jonbuford/atomo-all-boards/CM_M2K22_A/prod/CM_M2K22_A-F.Mask.pdf

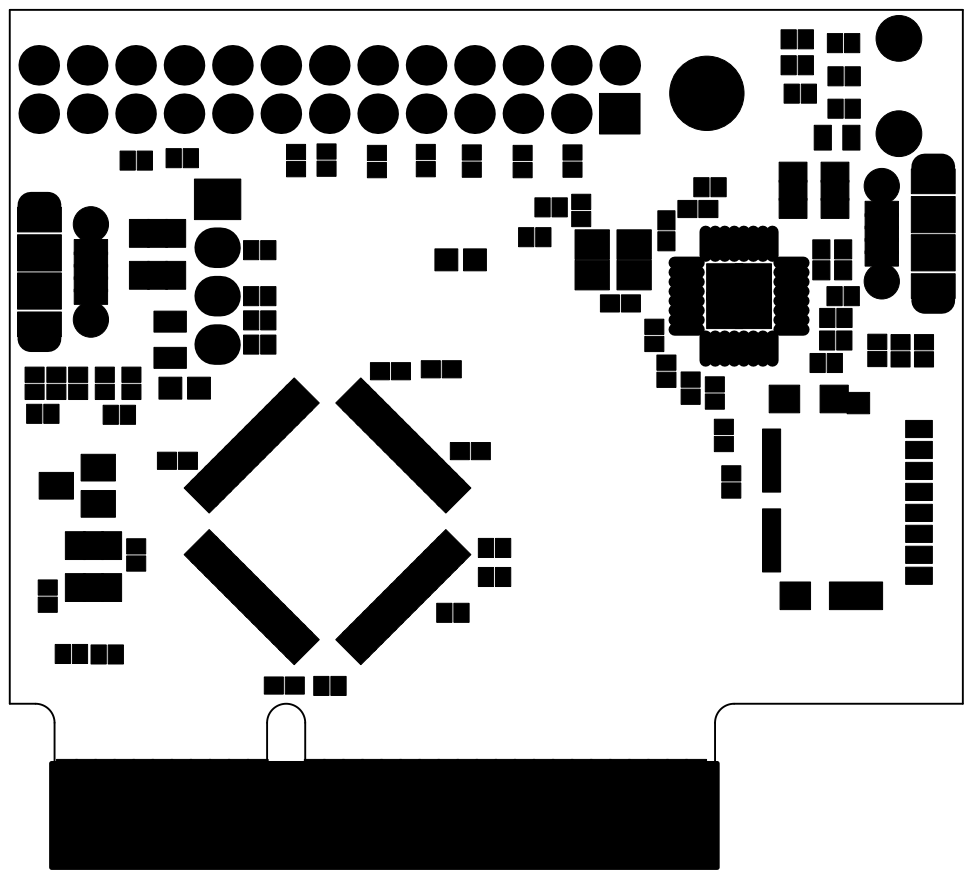
[picture p11: page 1]
