jonbuford/atomo-all-boards/CM_M2K22_A/prod/CM_M2K22_A-F.Paste.pdf

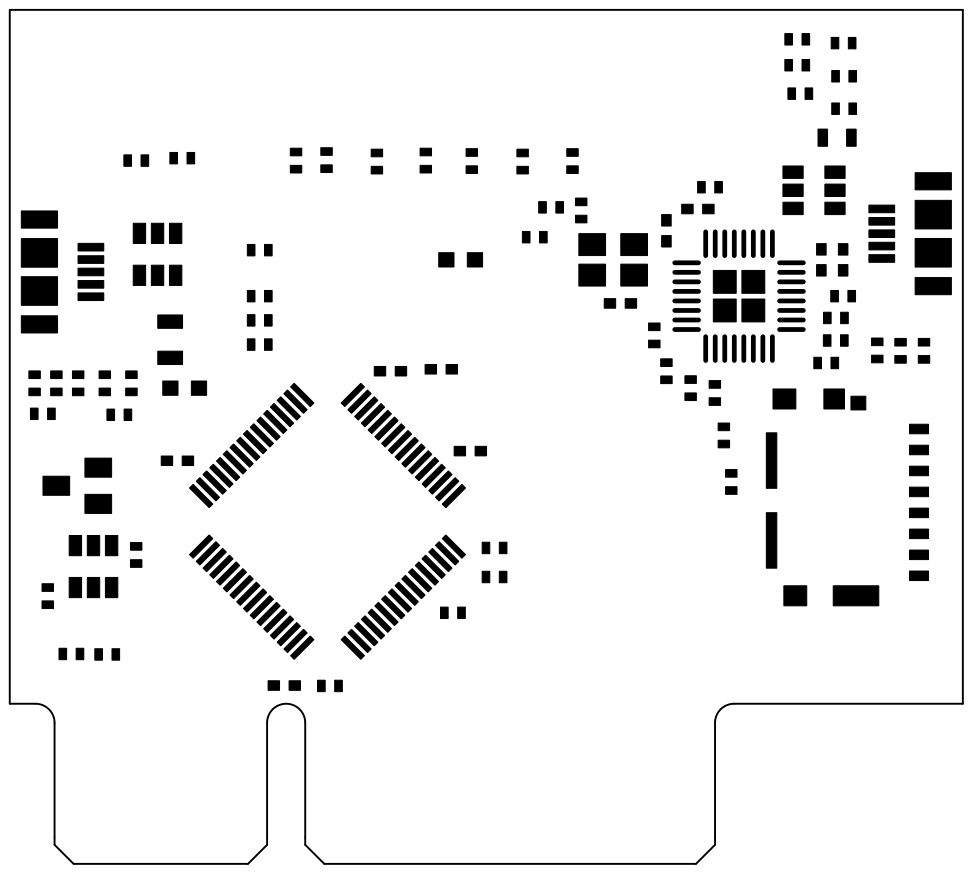
[picture p12: page 1]
