jonbuford/atomo-all-boards/CM_M2K22_A/prod/CM_M2K22_A-F.SilkS.pdf

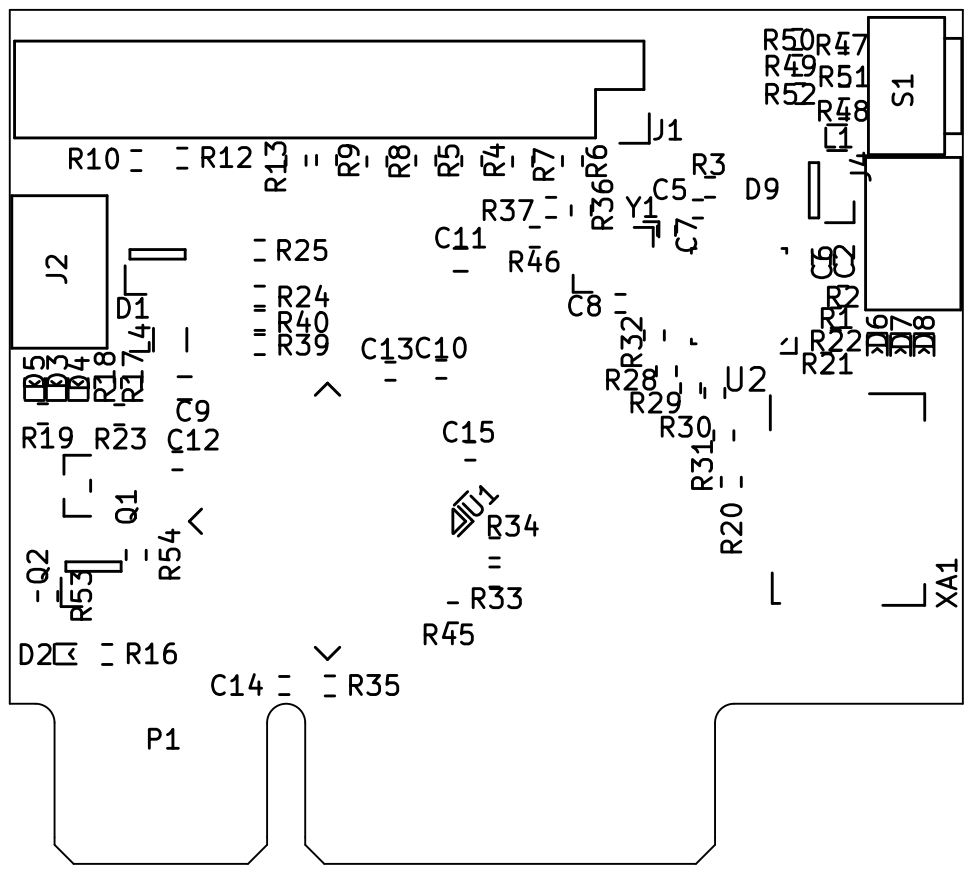
[picture p13: page 1]
