jonbuford/atomo-all-boards/CM_M2K22_A/prod/CM_M2K22_A-In1.Cu.pdf

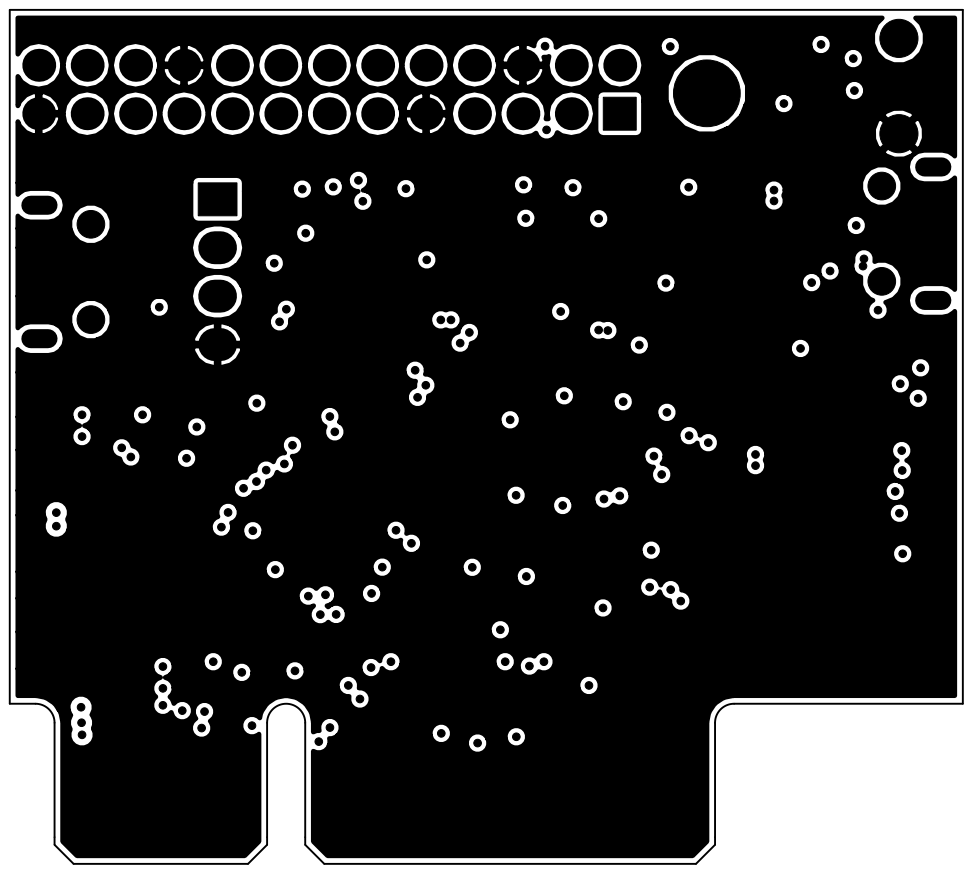
[picture p14: page 1]
