jonbuford/atomo-all-boards/CM_M2K22_A/prod/CM_M2K22_A-In2.Cu.pdf

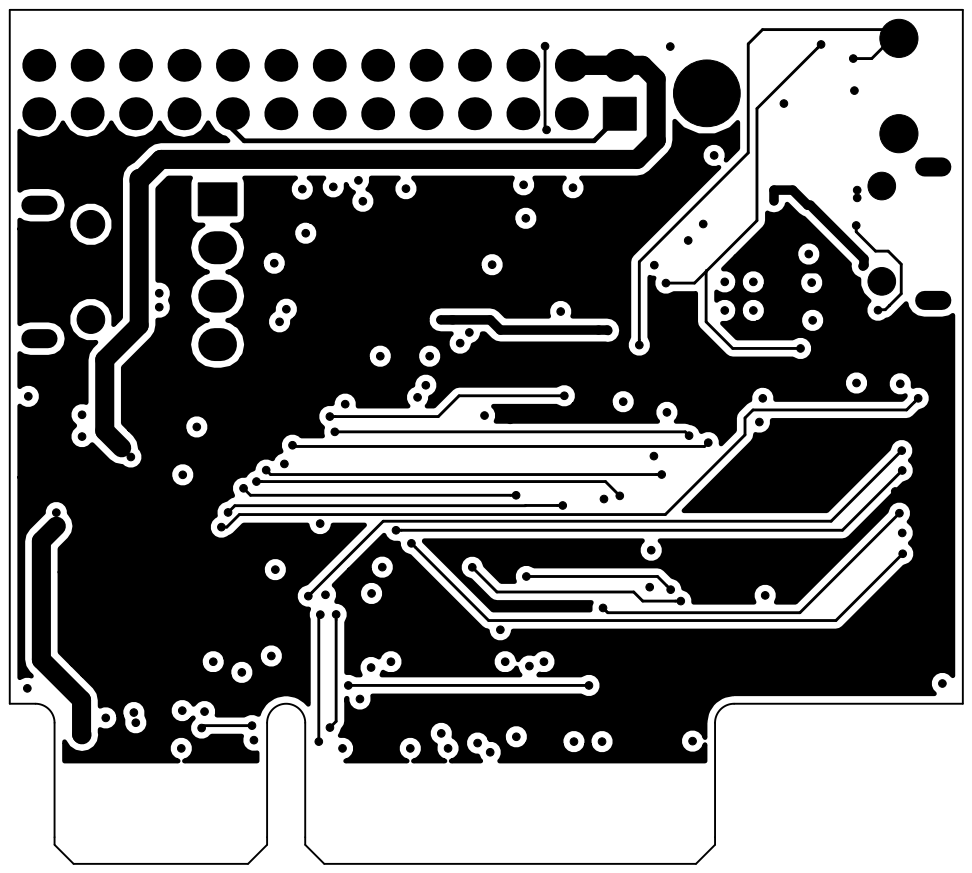
[picture p15: page 1]
