jonbuford/atomo-all-boards/CM_M4K64_A/prod/CM_M4K64_A-B.Adhes.pdf

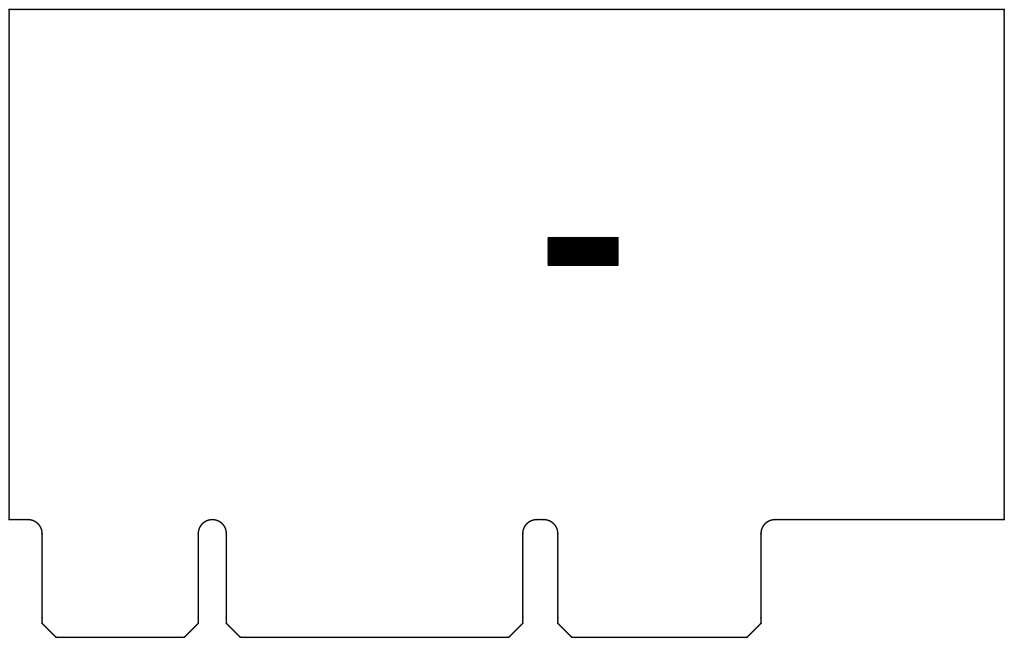
[picture p16: page 1]
