jonbuford/atomo-all-boards/CM_M4K64_A/prod/CM_M4K64_A-B.Cu.pdf

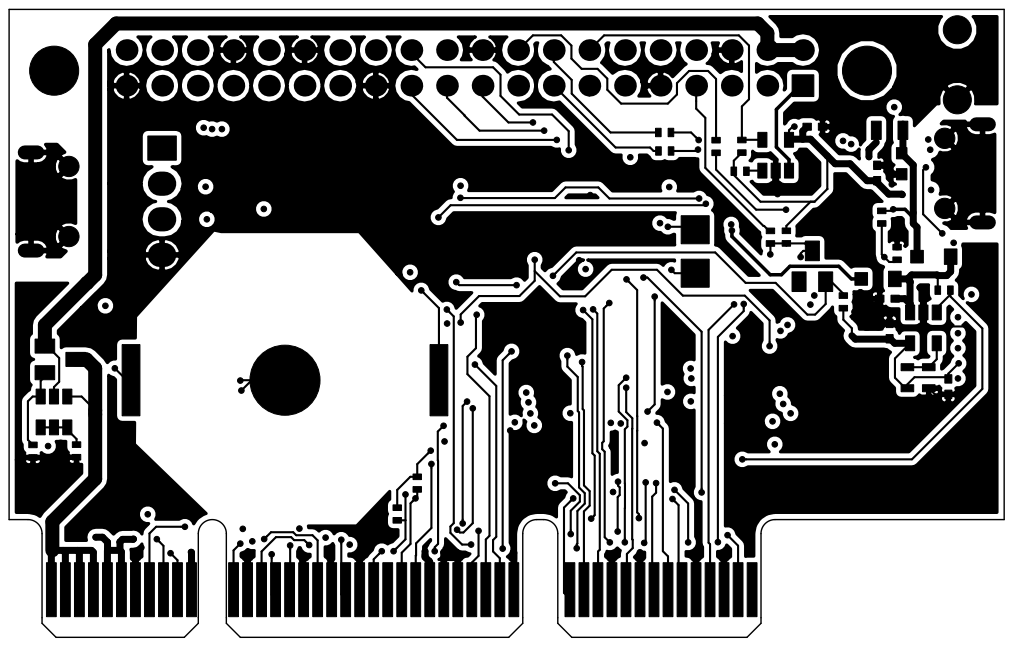
[picture p17: page 1]
