jonbuford/atomo-all-boards/CM_M4K64_A/prod/CM_M4K64_A-B.Mask.pdf

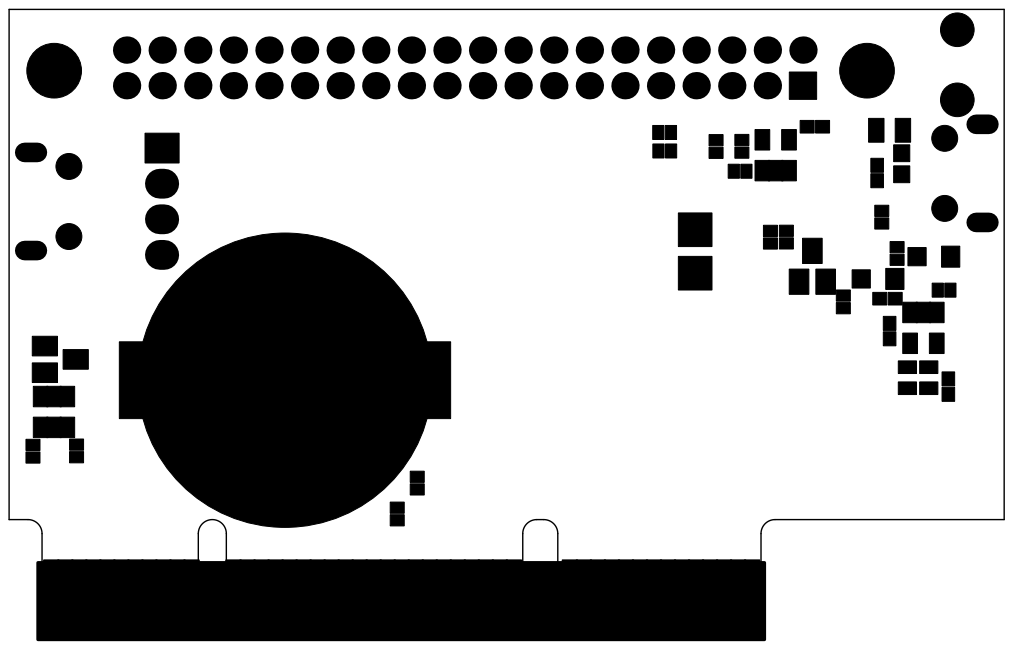
[picture p18: page 1]
