jonbuford/atomo-all-boards/CM_M4K64_A/prod/CM_M4K64_A-B.Paste.pdf

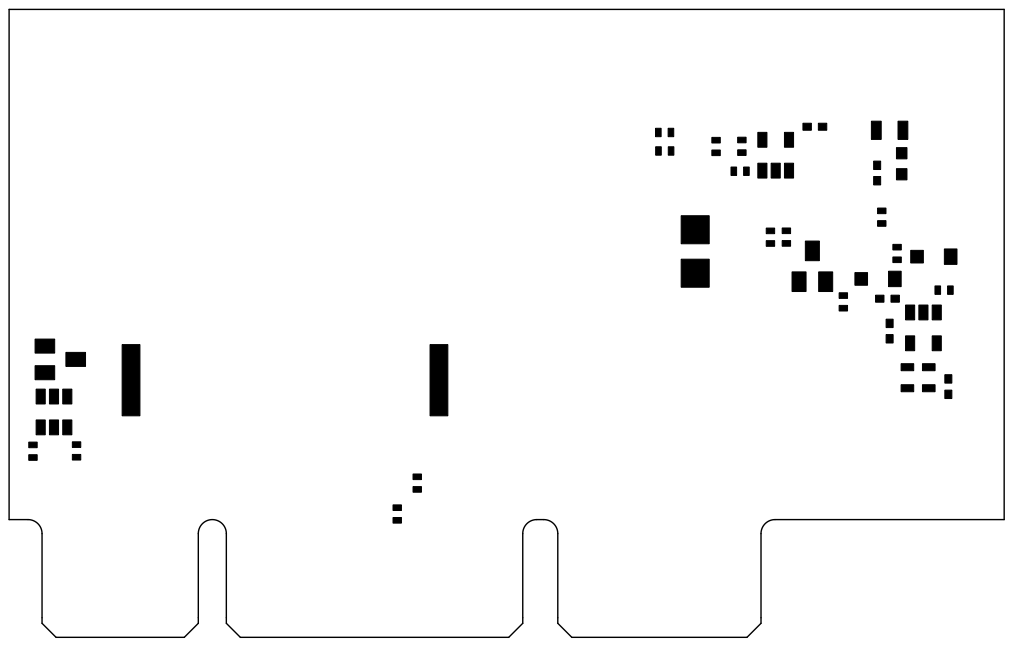
[picture p19: page 1]
