jonbuford/atomo-all-boards/CM_M4K64_A/prod/CM_M4K64_A-B.SilkS.pdf

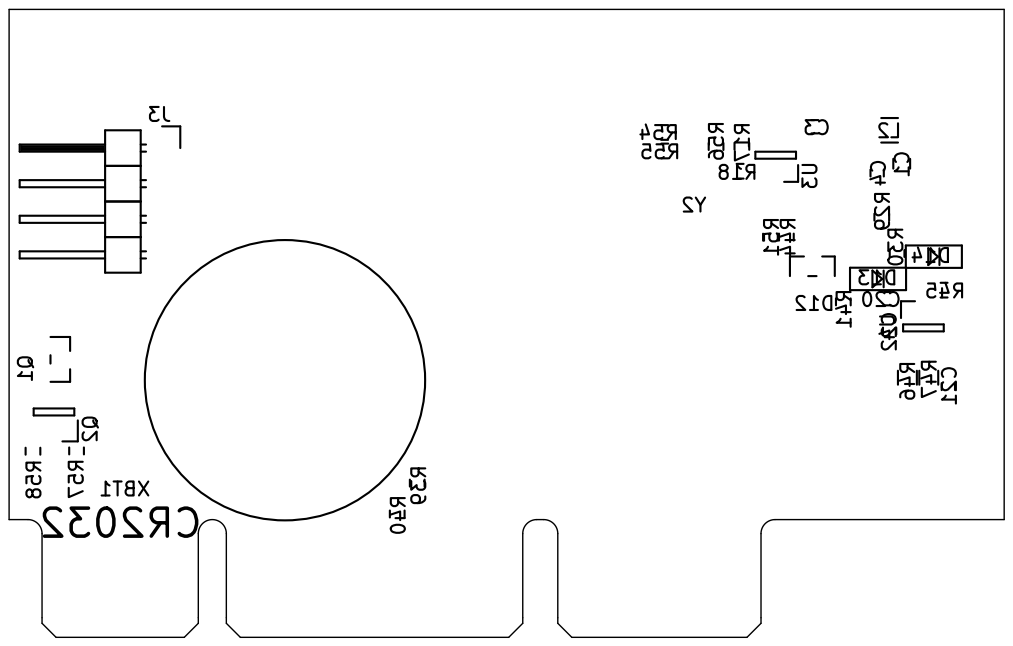
[picture p20: page 1]
