jonbuford/atomo-all-boards/CM_M4K64_A/prod/CM_M4K64_A-Edge.Cuts.pdf

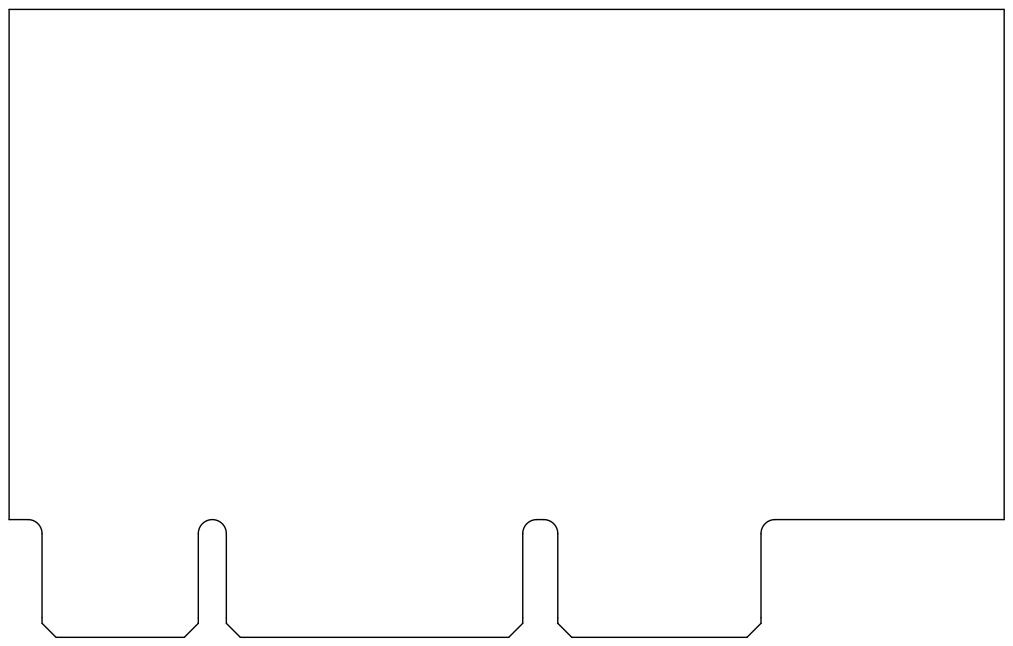
[picture p21: page 1]
