jonbuford/atomo-all-boards/CM_M4K64_A/prod/CM_M4K64_A-F.Cu.pdf

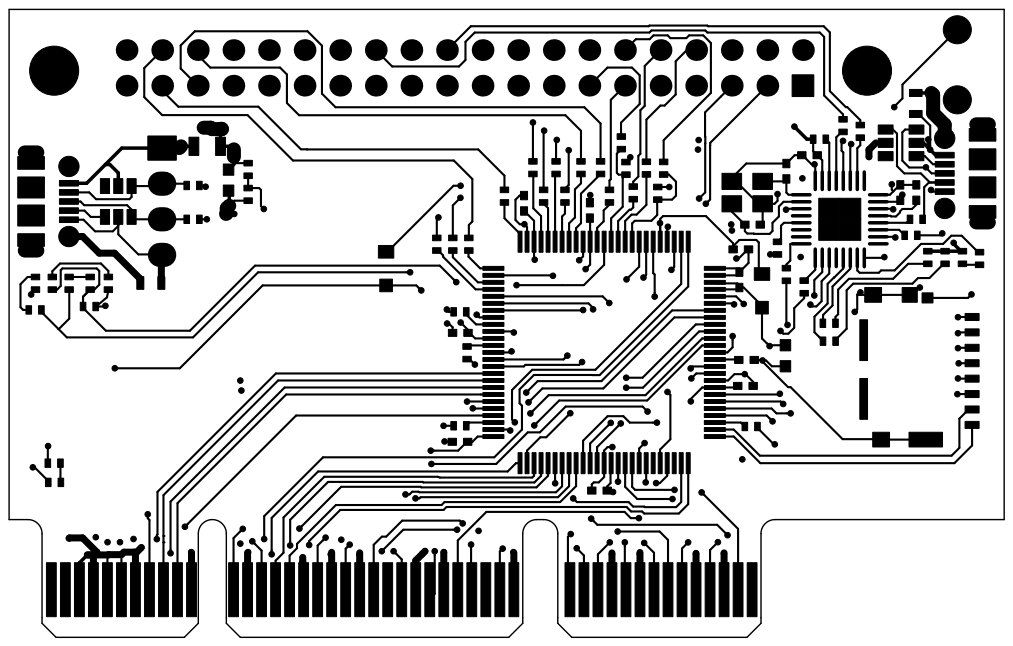
[picture p22: page 1]
