jonbuford/atomo-all-boards/CM_M4K64_A/prod/CM_M4K64_A-F.Mask.pdf

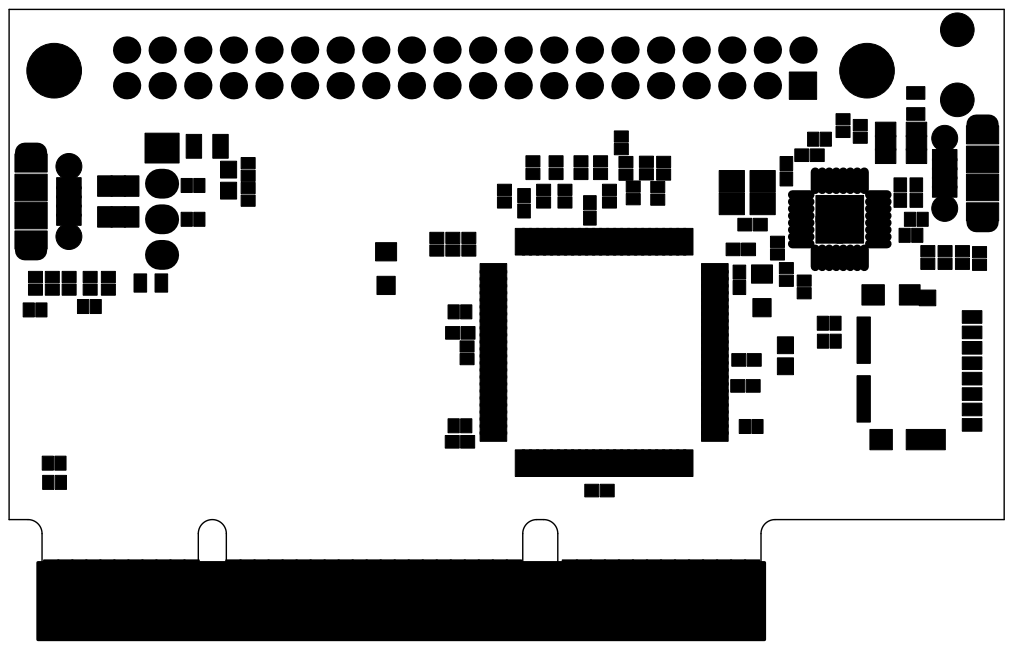
[picture p23: page 1]
