jonbuford/atomo-all-boards/CM_M4K64_A/prod/CM_M4K64_A-F.Paste.pdf

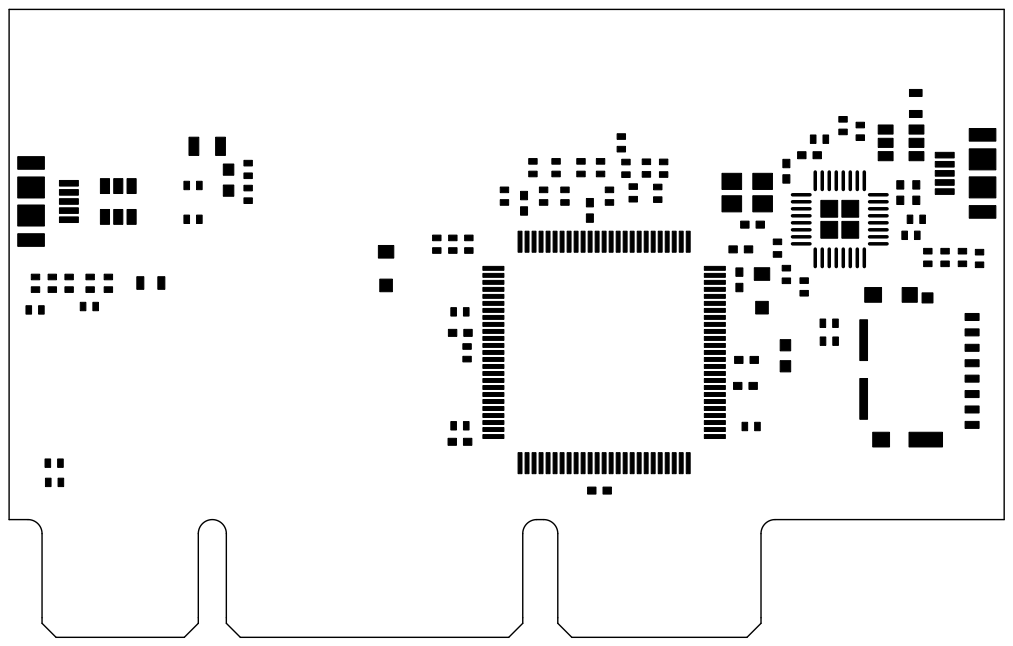
[picture p24: page 1]
