jonbuford/atomo-all-boards/CM_M4K64_A/prod/CM_M4K64_A-F.SilkS.pdf

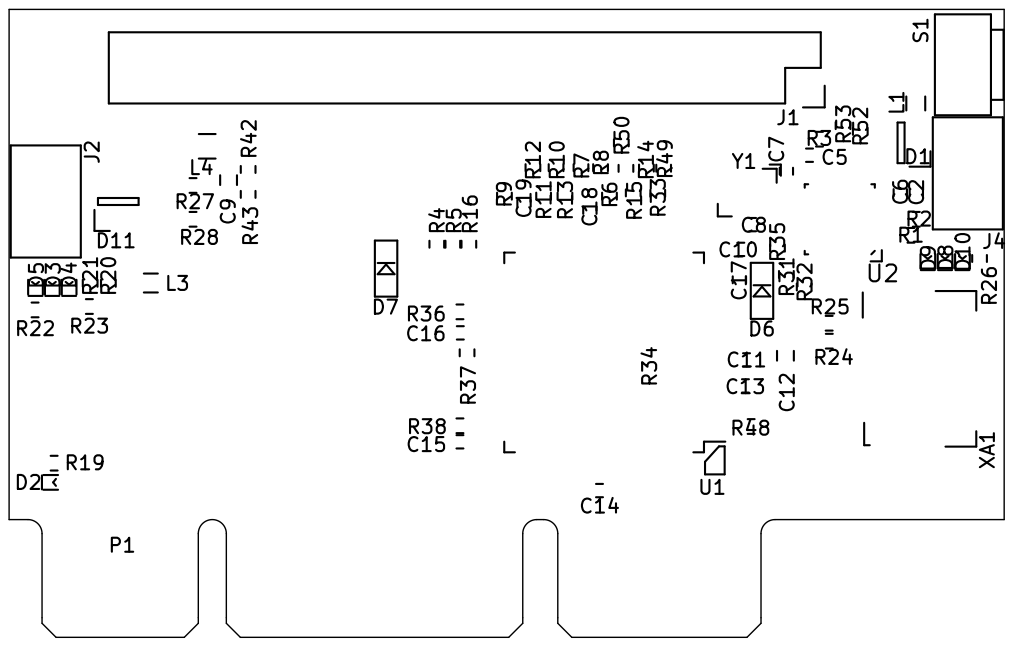
[picture p25: page 1]
