jonbuford/atomo-all-boards/CM_M4K64_A/prod/CM_M4K64_A-In1.Cu.pdf

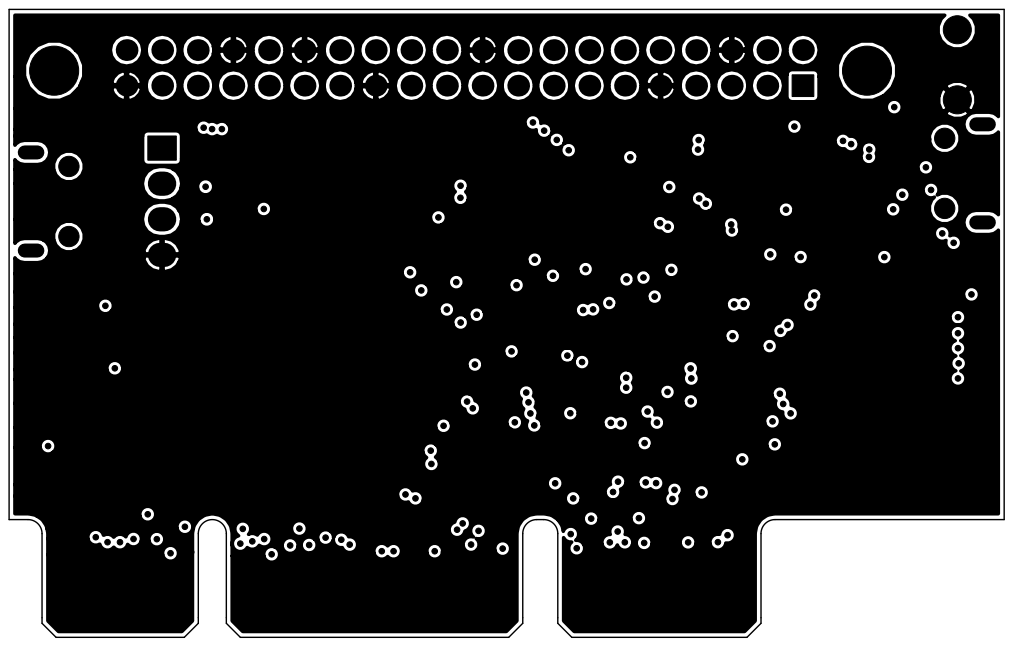
[picture p26: page 1]
