jonbuford/atomo-all-boards/CM_M4K64_A/prod/CM_M4K64_A-In2.Cu.pdf

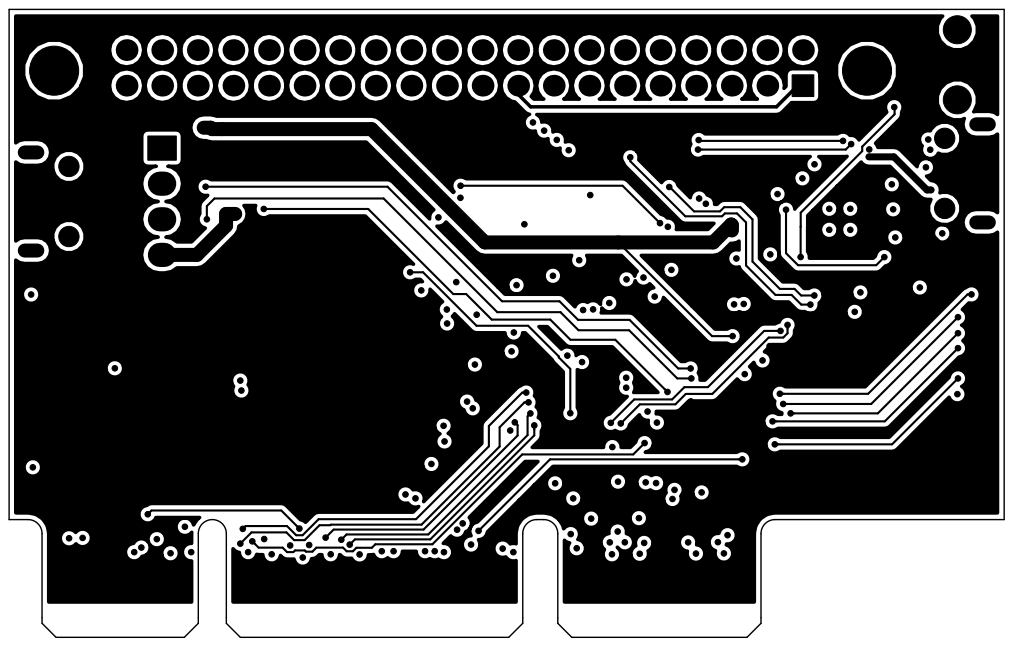
[picture p27: page 1]
