jonbuford/atomo-all-boards/CM_M8K64_A/prod/CM_M8K64_A-B.Adhes.pdf

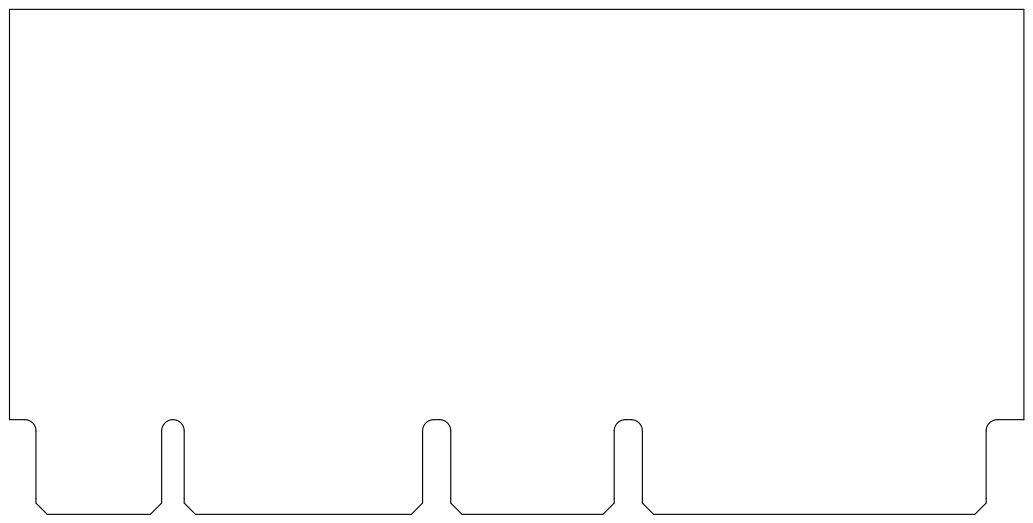
[picture p28: page 1]
