jonbuford/atomo-all-boards/CM_M8K64_A/prod/CM_M8K64_A-B.Cu.pdf

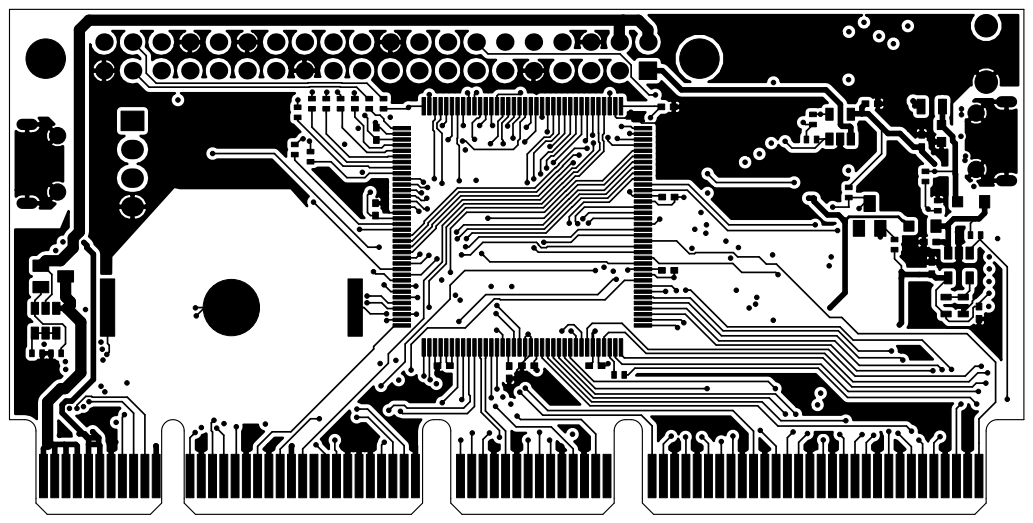
[picture p29: page 1]
