jonbuford/atomo-all-boards/CM_M8K64_A/prod/CM_M8K64_A-B.Mask.pdf

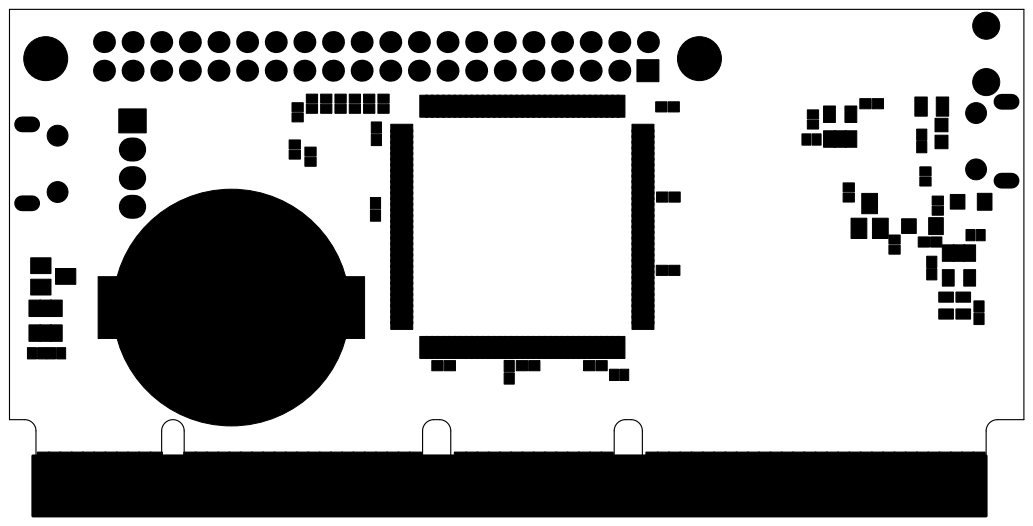
[picture p30: page 1]
