jonbuford/atomo-all-boards/CM_M8K64_A/prod/CM_M8K64_A-B.Paste.pdf

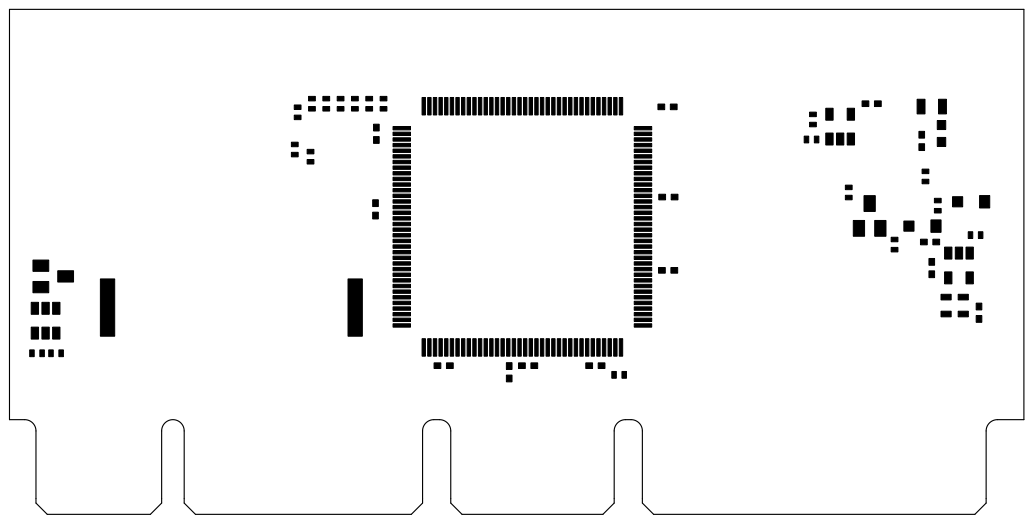
[picture p31: page 1]
