jonbuford/atomo-all-boards/CM_M8K64_A/prod/CM_M8K64_A-B.SilkS.pdf

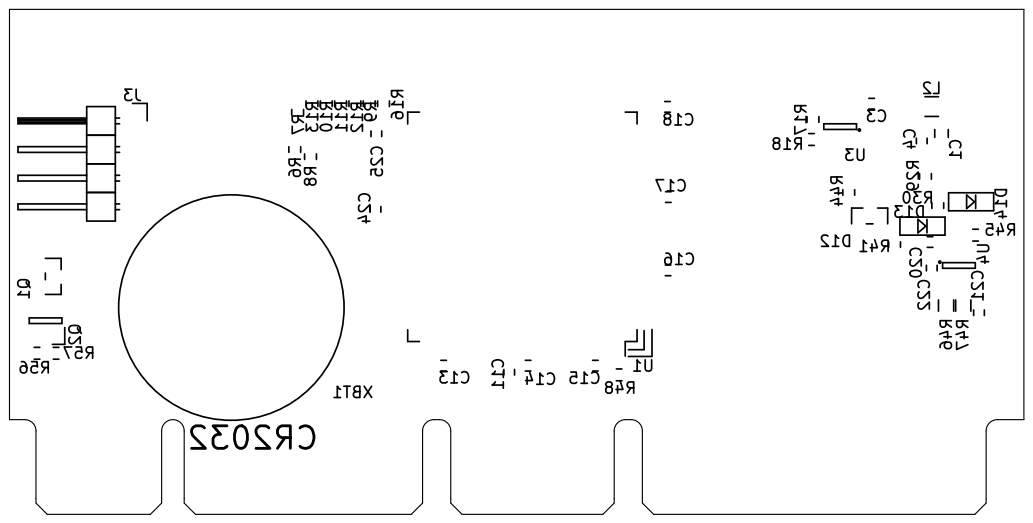
[picture p32: page 1]
