jonbuford/atomo-all-boards/CM_M8K64_A/prod/CM_M8K64_A-F.Adhes.pdf

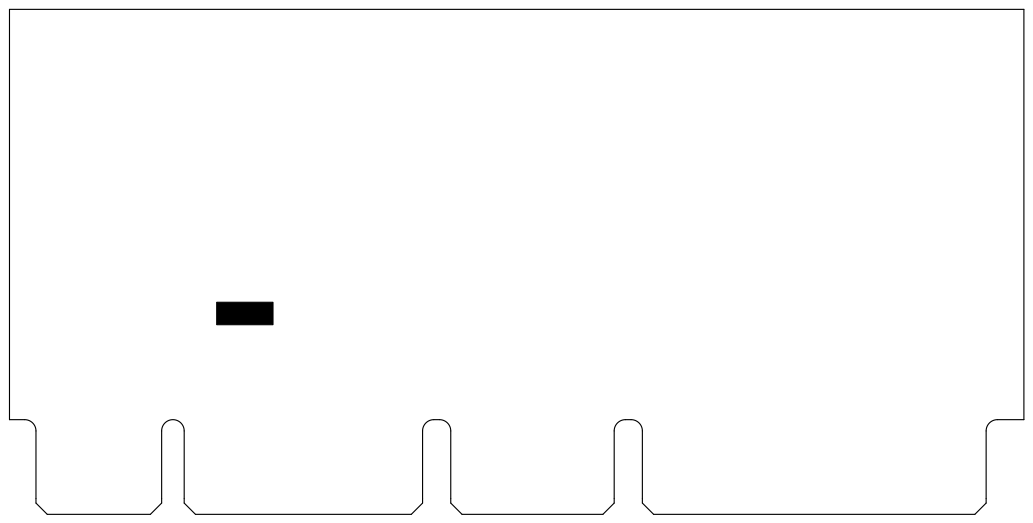
[picture p33: page 1]
