jonbuford/atomo-all-boards/CM_M8K64_A/prod/CM_M8K64_A-F.Cu.pdf

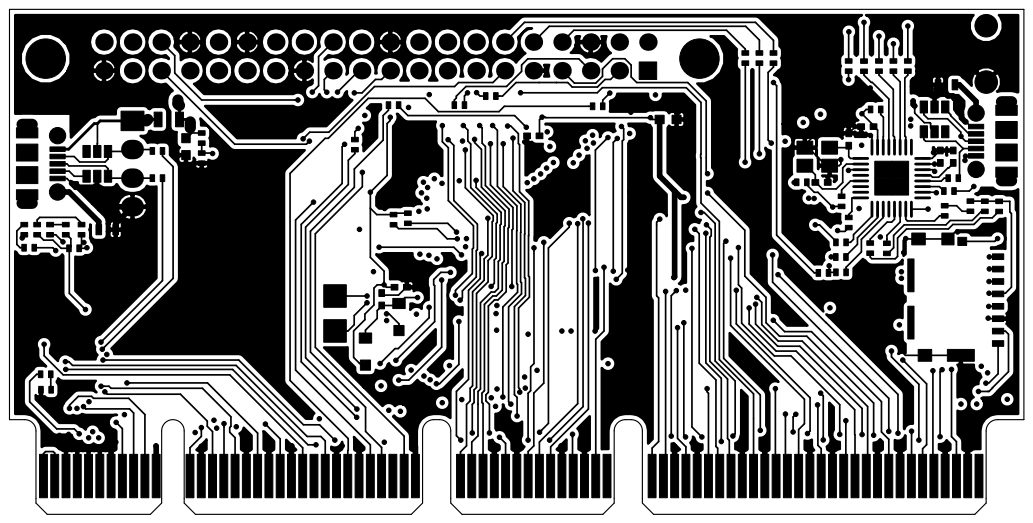
[picture p34: page 1]
