jonbuford/atomo-all-boards/CM_M8K64_A/prod/CM_M8K64_A-F.Mask.pdf

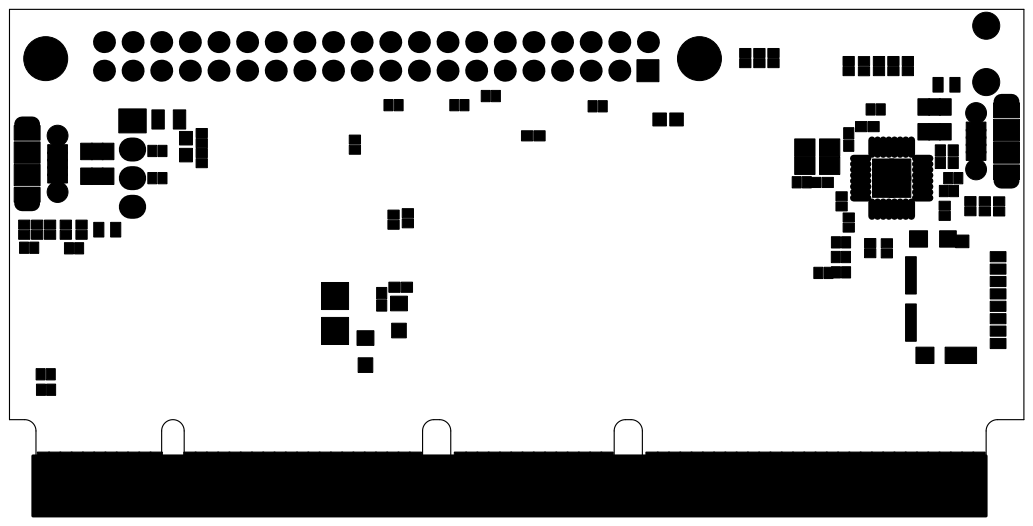
[picture p35: page 1]
