jonbuford/atomo-all-boards/CM_M8K64_A/prod/CM_M8K64_A-F.Paste.pdf

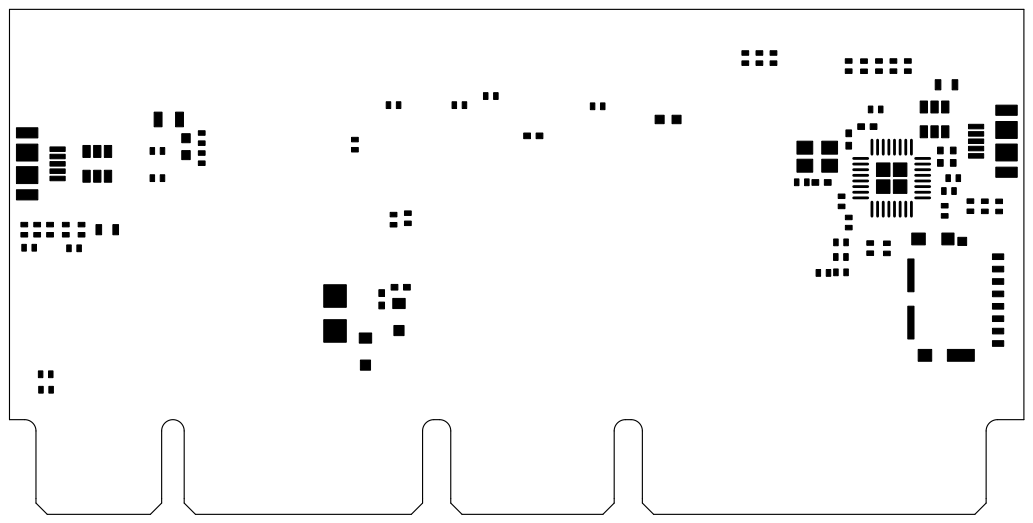
[picture p36: page 1]
