jonbuford/atomo-all-boards/CM_M8K64_A/prod/CM_M8K64_A-F.SilkS.pdf

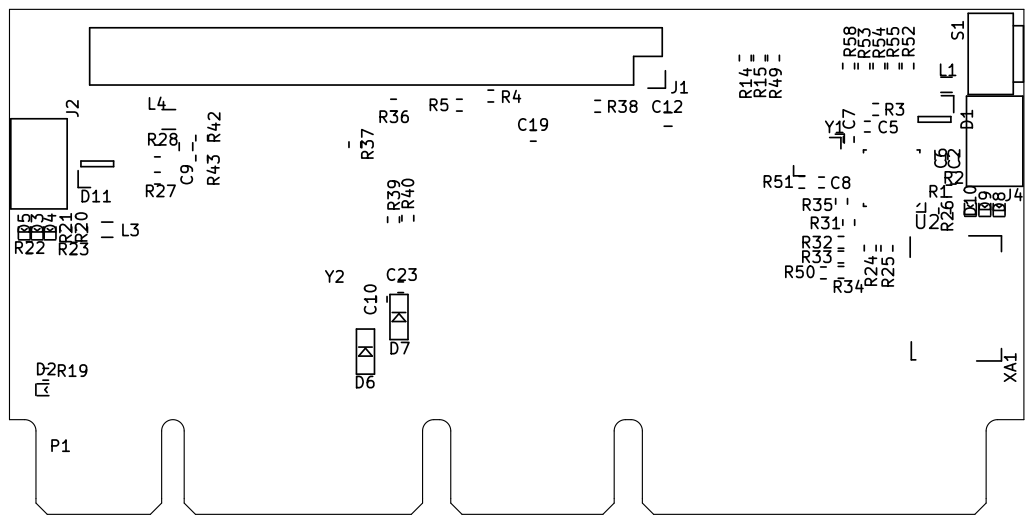
[picture p37: page 1]
