jonbuford/atomo-all-boards/CM_M8K64_A/prod/CM_M8K64_A-In1.Cu.pdf

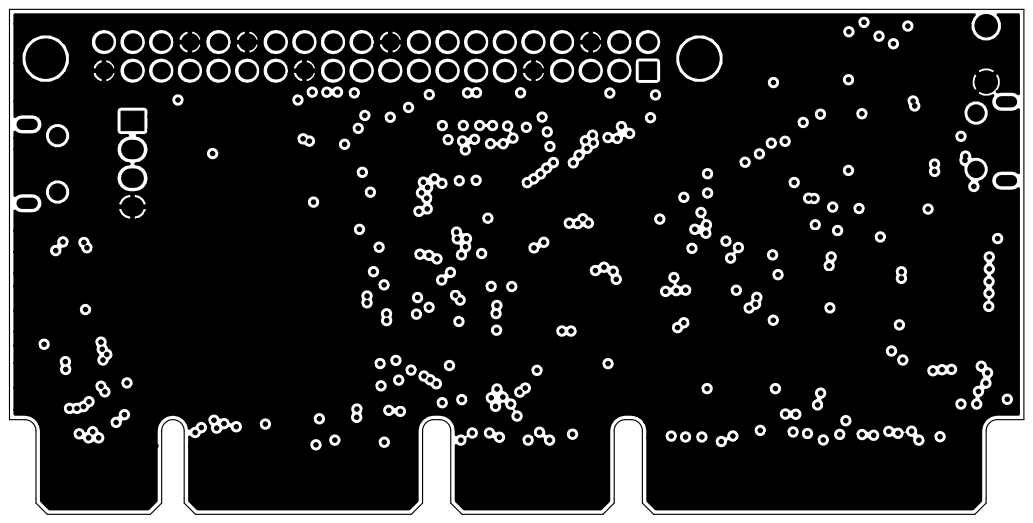
[picture p38: page 1]
