jonbuford/atomo-all-boards/CM_M8K64_A/prod/CM_M8K64_A-In2.Cu.pdf

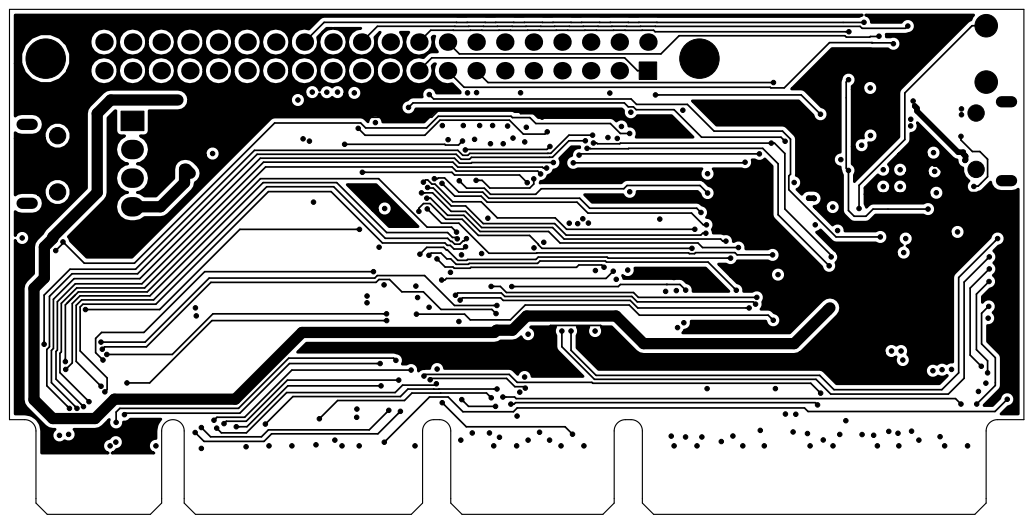
[picture p39: page 1]
