jonbuford/atomo-all-boards/EM_ETHUSB_01_A/prod/EM-ETHUSB-01-A-B.Cu.pdf

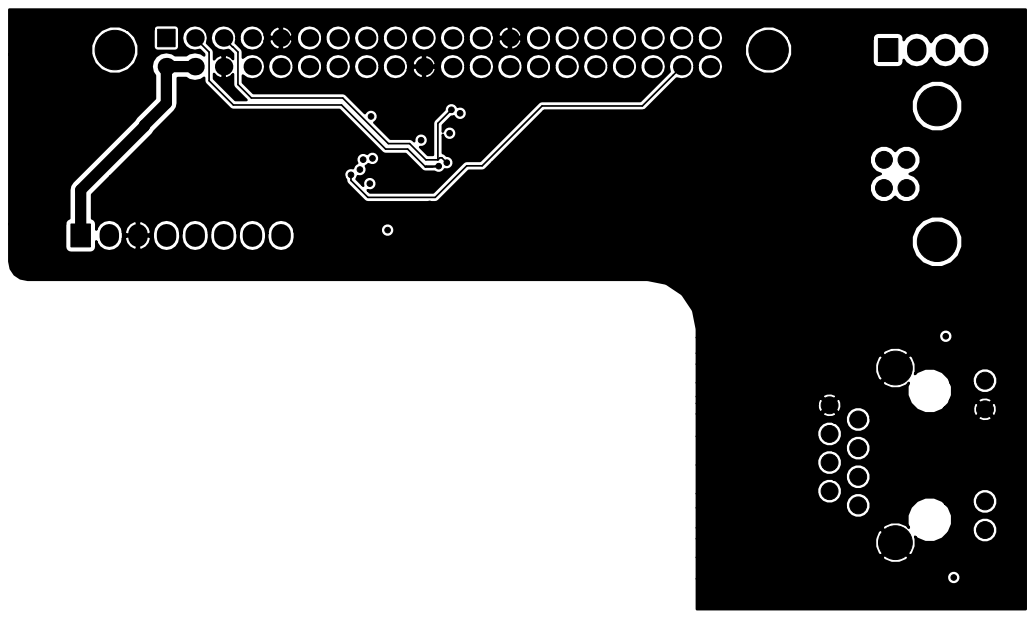
[picture p40: page 1]
