jonbuford/atomo-all-boards/EM_ETHUSB_01_A/prod/EM-ETHUSB-01-A-B.Mask.pdf

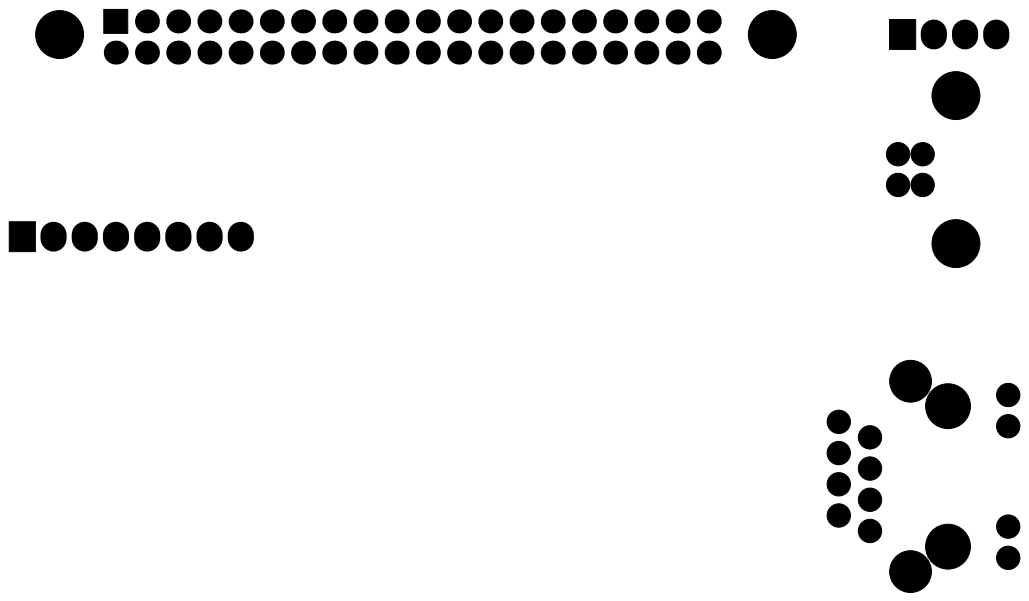
[picture p41: page 1]
