jonbuford/atomo-all-boards/EM_ETHUSB_01_A/prod/EM-ETHUSB-01-A-Edge.Cuts.pdf

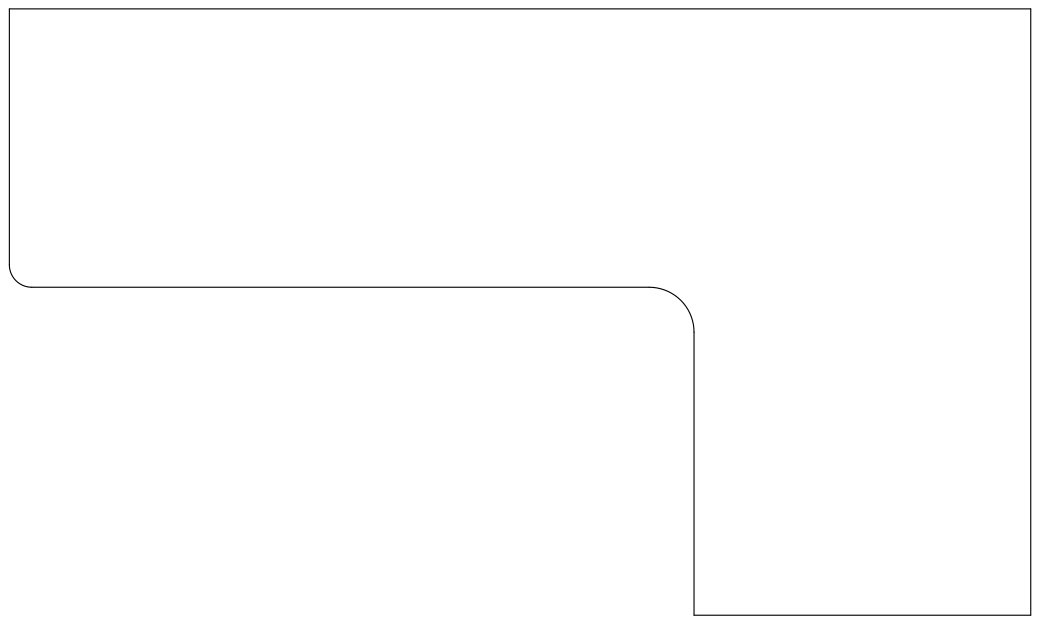
[picture p42: page 1]
