jonbuford/atomo-all-boards/EM_ETHUSB_01_A/prod/EM-ETHUSB-01-A-F.Cu.pdf

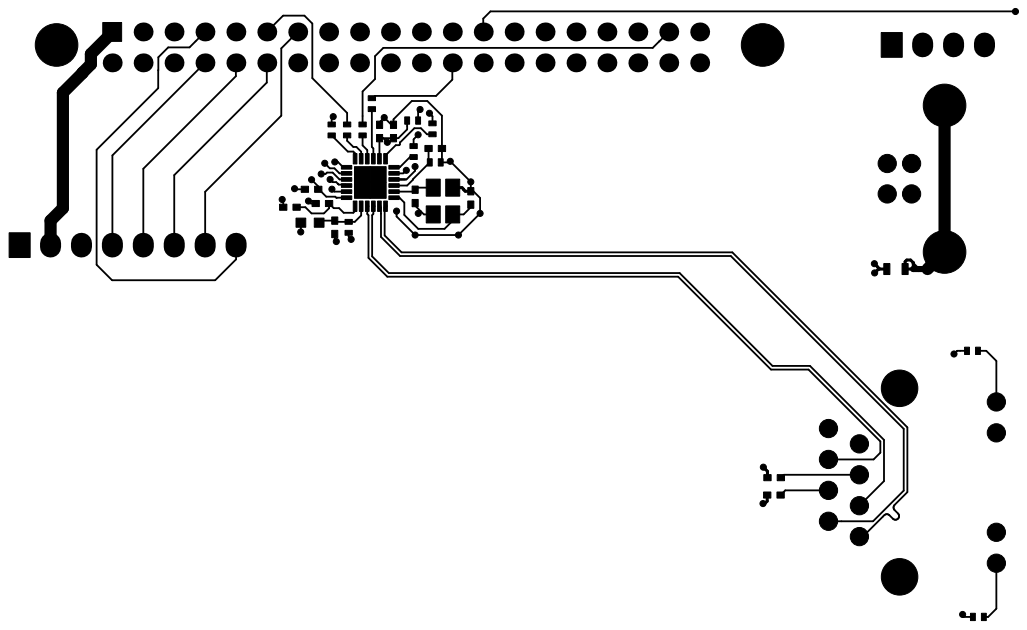
[picture p43: page 1]
