jonbuford/atomo-all-boards/EM_ETHUSB_01_A/prod/EM-ETHUSB-01-A-F.Mask.pdf

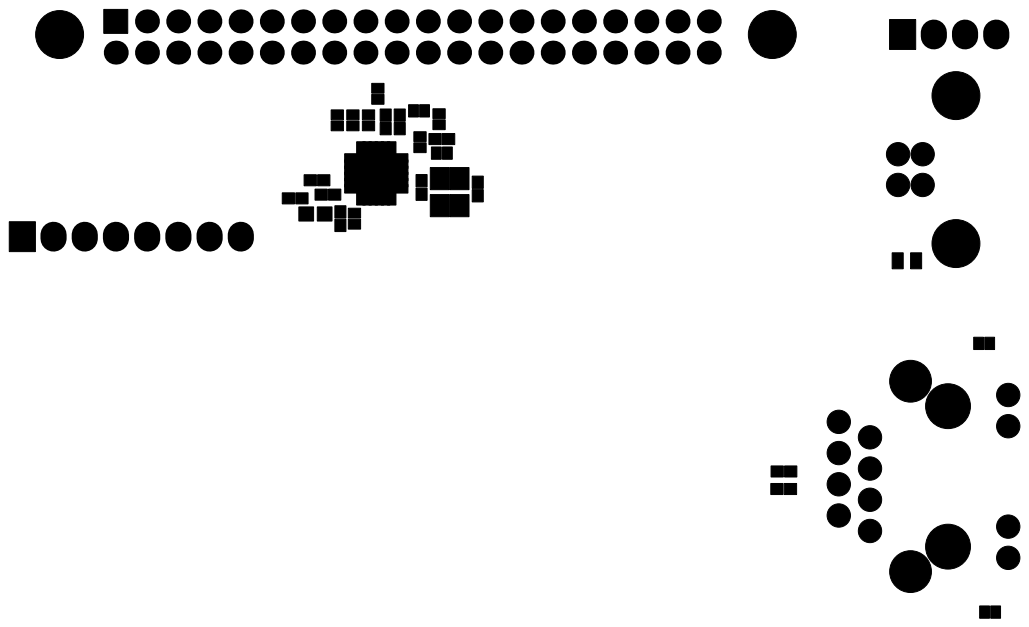
[picture p44: page 1]
