jonbuford/atomo-all-boards/EM_ETHUSB_01_A/prod/EM-ETHUSB-01-A-F.Paste.pdf

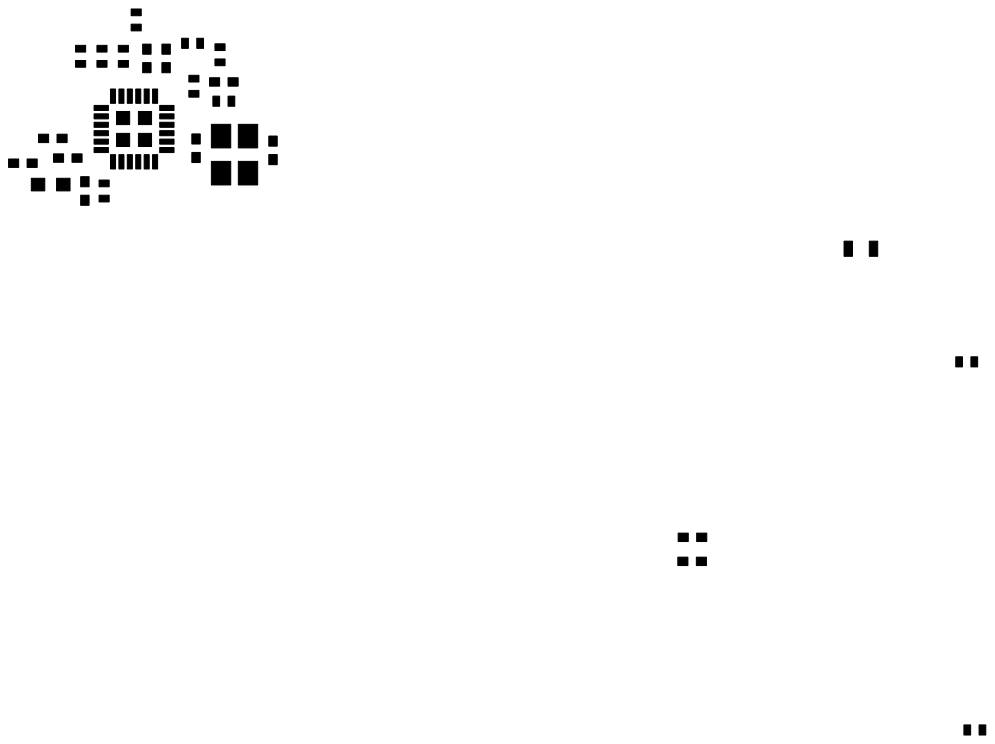
[picture p45: page 1]
