jonbuford/atomo-all-boards/EM_ETHUSB_01_A/prod/EM-ETHUSB-01-A-F.SilkS.pdf

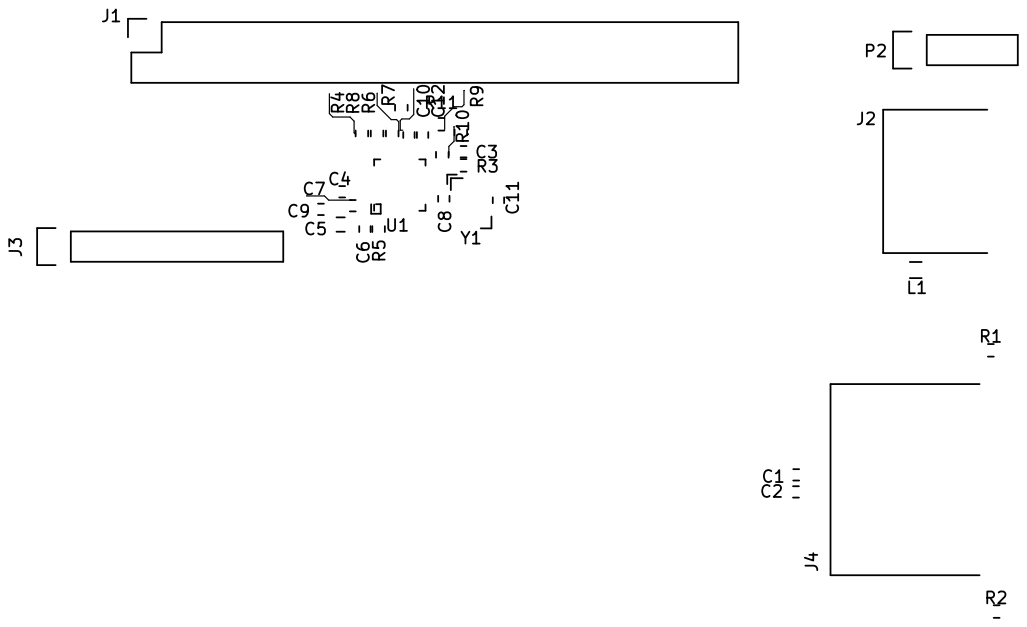
[picture p46: page 1]
