jonbuford/atomo-all-boards/EM_ETHUSB_01_A/prod/EM-ETHUSB-01-A-In1.Cu.pdf

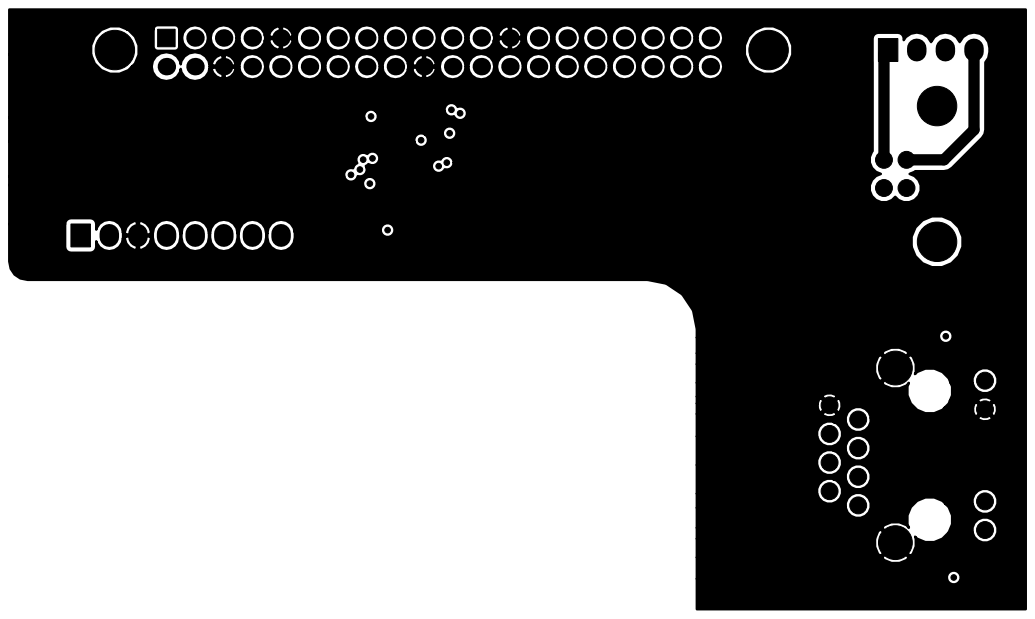
[picture p47: page 1]
