jonbuford/atomo-all-boards/EM_ETHUSB_01_A/prod/EM-ETHUSB-01-A-In2.Cu.pdf

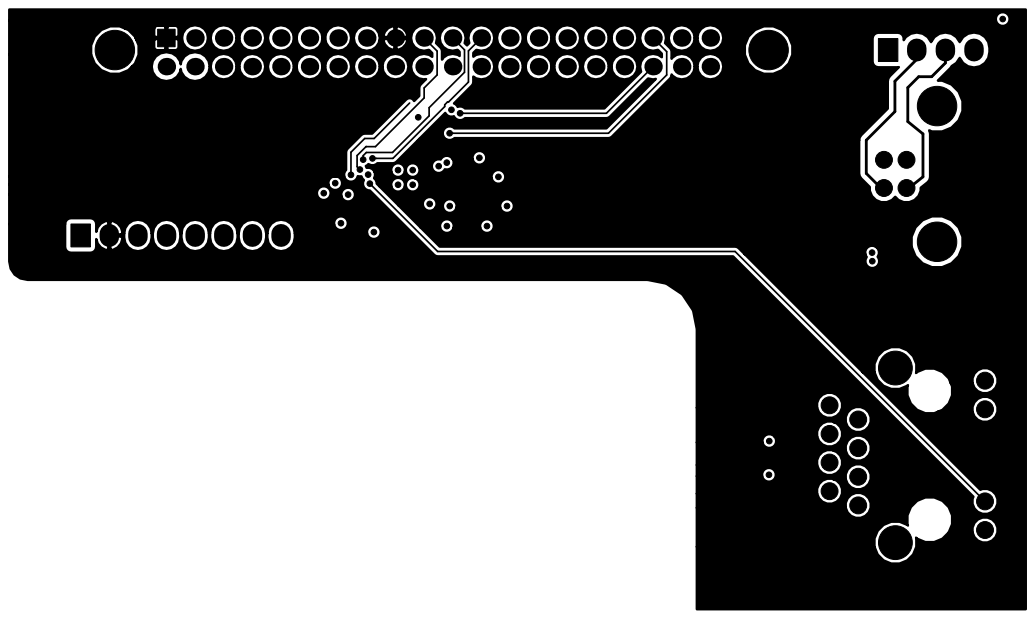
[picture p48: page 1]
